jack-union/mini-speedo/00_logo.ino

/*
 * Logo definition
 *
 */
//----Define Logo-------
/*
#define LOGO_HEIGHT   30
#define LOGO_WIDTH    67

static const unsigned char PROGMEM logo_bmp[] = {
   0x00, 0x00, 0x00, 0xff, 0xff, 0xff, 0x1f, 0x00, 0x00, 0x00, 0x00, 0x80,
   0xff, 0xff, 0xff, 0x7f, 0x00, 0x00, 0x00, 0x00, 0xc0, 0x01, 0x00, 0x00,
   0xe0, 0x00, 0x00, 0x00, 0x00, 0xe0, 0x00, 0x00, 0x00, 0xc0, 0x01, 0x00,
   0x00, 0x00, 0x60, 0x00, 0x00, 0x00, 0x80, 0x03, 0x00, 0x00, 0x00, 0x70,
   0x00, 0x00, 0x00, 0x00, 0x07, 0x00, 0x00, 0x00, 0x30, 0x00, 0x00, 0x00,
   0x00, 0x06, 0x00, 0x00, 0x00, 0x18, 0x00, 0x00, 0x00, 0x00, 0x0e, 0x00,
   0x00, 0x00, 0x0c, 0x00, 0x00, 0x00, 0x00, 0x1c, 0x00, 0x00, 0x00, 0x0f,
   0x00, 0x00, 0x00, 0x00, 0x18, 0x00, 0xf0, 0xff, 0x07, 0x00, 0x00, 0x00,
   0x00, 0x30, 0x00, 0xfc, 0xff, 0x00, 0x00, 0x00, 0x00, 0x00, 0x70, 0x00,
   0x0e, 0x00, 0x00, 0x00, 0x00, 0x00, 0x00, 0xe0, 0x00, 0x07, 0x00, 0x00,
   0x00, 0x00, 0x00, 0x00, 0xc0, 0x01, 0x03, 0x00, 0x00, 0x00, 0x00, 0x00,
   0x00, 0x80, 0x01, 0x03, 0x00, 0x00, 0x00, 0x00, 0x00, 0x00, 0x00, 0x03,
   0x03, 0x00, 0x00, 0x00, 0x00, 0x00, 0x00, 0x00, 0x03, 0x03, 0x00, 0x00,
   0x00, 0x00, 0x00, 0x00, 0x00, 0x07, 0x86, 0x07, 0x00, 0x00, 0x00, 0x00,
   0xe0, 0x03, 0x06, 0xe6, 0x1c, 0x00, 0x00, 0x00, 0x00, 0x70, 0x07, 0x06,
   0x36, 0x30, 0x00, 0x00, 0x00, 0x00, 0x18, 0x0c, 0x06, 0x16, 0x20, 0x00,
   0x00, 0x00, 0x00, 0x0c, 0x18, 0x03, 0x1e, 0x60, 0x00, 0x00, 0x00, 0x00,
   0x04, 0x10, 0x03, 0x0e, 0x40, 0x00, 0x00, 0x00, 0x00, 0x06, 0xb0, 0x03,
   0x0c, 0xc0, 0xff, 0xff, 0xff, 0xff, 0x07, 0xf0, 0x00, 0x1c, 0xe0, 0xff,
   0xff, 0xff, 0xff, 0x07, 0x70, 0x00, 0x18, 0x20, 0x00, 0x00, 0x00, 0x00,
   0x0c, 0x18, 0x00, 0x30, 0x30, 0x00, 0x00, 0x00, 0x00, 0x18, 0x08, 0x00,
   0x60, 0x18, 0x00, 0x00, 0x00, 0x00, 0x30, 0x0e, 0x00, 0xc0, 0x0f, 0x00,
   0x00, 0x00, 0x00, 0xe0, 0x03, 0x00 };
*/
//----End Define Logo-------
