jack-union/mini-speedo/01_logo_van.ino

/*
   Logo definition

*/

//----Define Logo-------

#define LOGO_HEIGHT 30
#define LOGO_WIDTH 73

static const unsigned char PROGMEM logo_bmp[] = {
    0x00, 0x00, 0x00, 0xff, 0xff, 0xff, 0xff, 0x7f, 0x00, 0x00, 0x00, 0x00,
    0x80, 0xff, 0xff, 0xff, 0xff, 0xff, 0x01, 0x00, 0x00, 0x00, 0xc0, 0x01,
    0x00, 0x00, 0x00, 0x80, 0x03, 0x00, 0x00, 0x00, 0xe0, 0x00, 0x00, 0x00,
    0x00, 0x00, 0x07, 0x00, 0x00, 0x00, 0x60, 0x00, 0x00, 0x00, 0x00, 0x00,
    0x06, 0x00, 0x00, 0x00, 0x70, 0x00, 0x00, 0x00, 0x00, 0x00, 0x0e, 0x00,
    0x00, 0x00, 0x30, 0x00, 0x00, 0x00, 0x00, 0x00, 0x0c, 0x00, 0x00, 0x00,
    0x18, 0x00, 0x00, 0x00, 0x00, 0x00, 0x1c, 0x00, 0x00, 0x00, 0x0c, 0x00,
    0x00, 0x00, 0x00, 0x00, 0x18, 0x00, 0x00, 0x00, 0x0f, 0x00, 0x00, 0x00,
    0x00, 0x00, 0x38, 0x00, 0xf0, 0xff, 0x07, 0x00, 0x00, 0x00, 0x00, 0x00,
    0x30, 0x00, 0xfc, 0xff, 0x00, 0x00, 0x00, 0x00, 0x00, 0x00, 0x30, 0x00,
    0x0e, 0x00, 0x00, 0x00, 0x00, 0x00, 0x00, 0x00, 0x70, 0x00, 0x07, 0x00,
    0x00, 0x00, 0x00, 0x00, 0x00, 0x00, 0x60, 0x00, 0x03, 0x00, 0x00, 0x00,
    0x00, 0x00, 0x00, 0x00, 0xe0, 0x00, 0x03, 0x00, 0x00, 0x00, 0x00, 0x00,
    0x00, 0x00, 0xc0, 0x00, 0x03, 0x00, 0x00, 0x00, 0x00, 0x00, 0x00, 0x00,
    0xc0, 0x00, 0x03, 0x00, 0x00, 0x00, 0x00, 0x00, 0x00, 0x00, 0x80, 0x01,
    0x86, 0x07, 0x00, 0x00, 0x00, 0x00, 0x00, 0xf8, 0x80, 0x01, 0xe6, 0x1c,
    0x00, 0x00, 0x00, 0x00, 0x00, 0xdc, 0x81, 0x01, 0x36, 0x30, 0x00, 0x00,
    0x00, 0x00, 0x00, 0x06, 0x83, 0x01, 0x16, 0x20, 0x00, 0x00, 0x00, 0x00,
    0x00, 0x03, 0x86, 0x01, 0x1e, 0x60, 0x00, 0x00, 0x00, 0x00, 0x00, 0x01,
    0xc4, 0x01, 0x0e, 0x40, 0x00, 0x00, 0x00, 0x00, 0x80, 0x01, 0xcc, 0x00,
    0x0c, 0xc0, 0xff, 0xff, 0xff, 0xff, 0xff, 0x01, 0x7c, 0x00, 0x1c, 0xe0,
    0xff, 0xff, 0xff, 0xff, 0xff, 0x01, 0x3c, 0x00, 0x18, 0x20, 0x00, 0x00,
    0x00, 0x00, 0x00, 0x03, 0x06, 0x00, 0x30, 0x30, 0x00, 0x00, 0x00, 0x00,
    0x00, 0x06, 0x02, 0x00, 0x60, 0x18, 0x00, 0x00, 0x00, 0x00, 0x00, 0x8c,
    0x03, 0x00, 0xc0, 0x0f, 0x00, 0x00, 0x00, 0x00, 0x00, 0xf8, 0x00, 0x00};

//----End Define Logo-------
