jack-union/mini-speedo/02_warning.ino

/*
 * Warning Logo definition
 *
 */

//----Define Warning Logo-------
#define WARNING_X_POS 100
#define WARNING_Y_POS 15
#define WARNING_HEIGHT 18
#define WARNING_WIDTH 20

static const unsigned char PROGMEM warning_bmp[] = {
    0x00, 0x06, 0x00, 0x00, 0x0f, 0x00, 0x80, 0x19, 0x00, 0x80, 0x19,
    0x00, 0xc0, 0x30, 0x00, 0xc0, 0x30, 0x00, 0x60, 0x66, 0x00, 0x60,
    0x66, 0x00, 0x30, 0xc6, 0x00, 0x30, 0xc6, 0x00, 0x18, 0x86, 0x01,
    0x18, 0x86, 0x01, 0x0c, 0x00, 0x03, 0x0c, 0x06, 0x03, 0x06, 0x06,
    0x06, 0x06, 0x00, 0x06, 0xff, 0xff, 0x0f, 0xff, 0xff, 0x0f};

//----End Define Warning Logo-------
